CombineReality/Deck-X/Deck_X/STL_files/Display_Trays/with_inserts/dx_tray_50_r_0105.stl

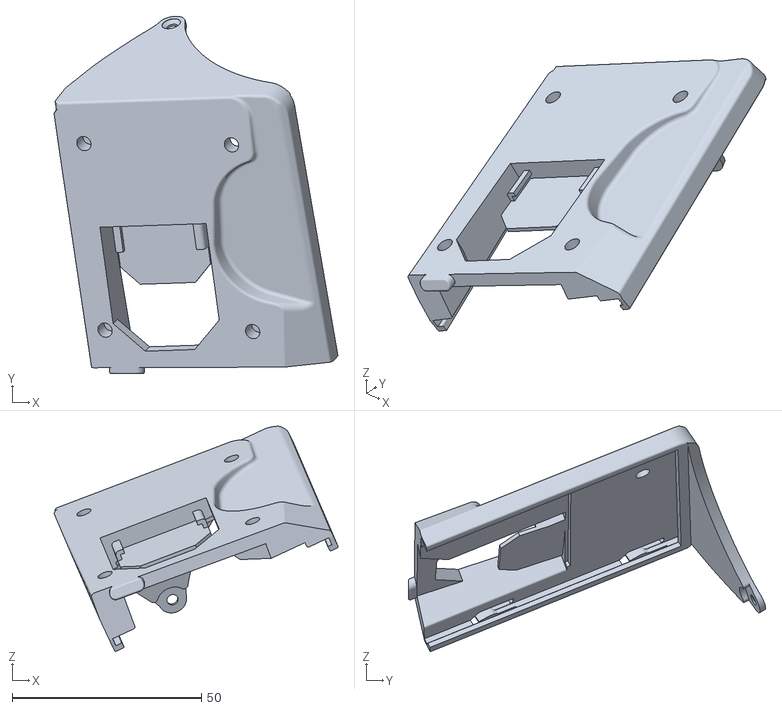
[picture p15: CAD file, 2021-03-06]
Deck_X/STL_files/Display_Trays/with_inserts/dx_tray_50_r_0105.stl
75.0 x 94.4 x 59.6
