CombineReality/Deck-X/Deck_X/STL_files/Headgear/dx_headgear_front_span.stl

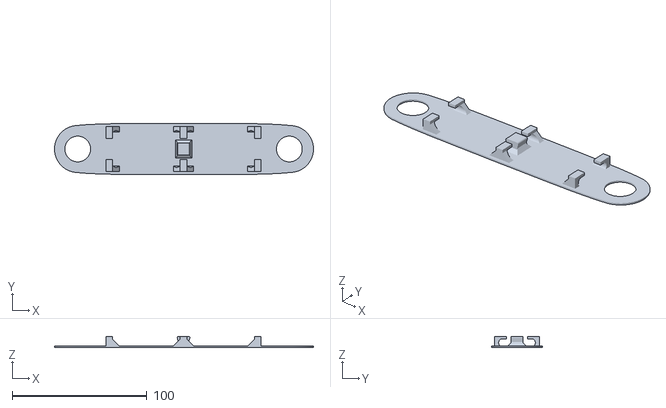
[picture p16: CAD file, 2021-03-06]
Deck_X/STL_files/Headgear/dx_headgear_front_span.stl
191.9 x 38.1 x 8.30
