CombineReality/Deck-X/Deck_X/STL_files/Headgear/Headgear_Pivots_(Print_2x)/dx_headgear_pivot_back_female.stl

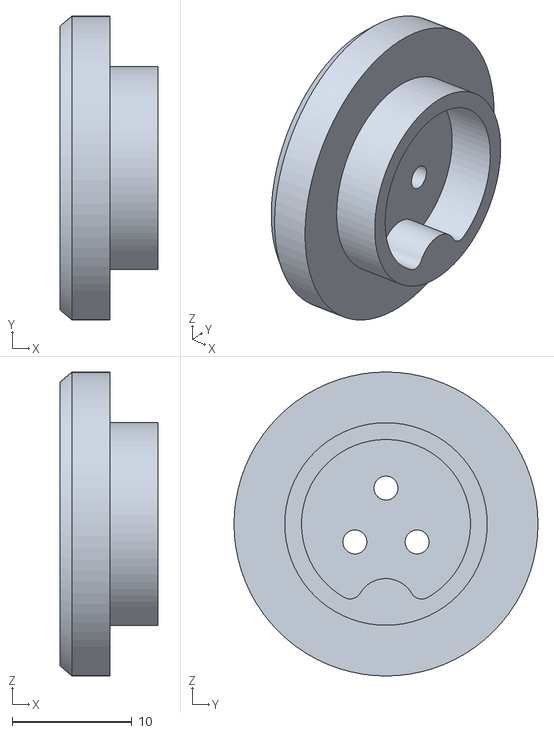
[picture p17: CAD file, 2021-03-06]
Deck_X/STL_files/Headgear/Headgear_Pivots_(Print_2x)/dx_headgear_pivot_back_female.stl
8.20 x 25.4 x 25.4
