CombineReality/Deck-X/Deck_X/STL_files/Lid_Assembly/dx_dpad_0105.stl

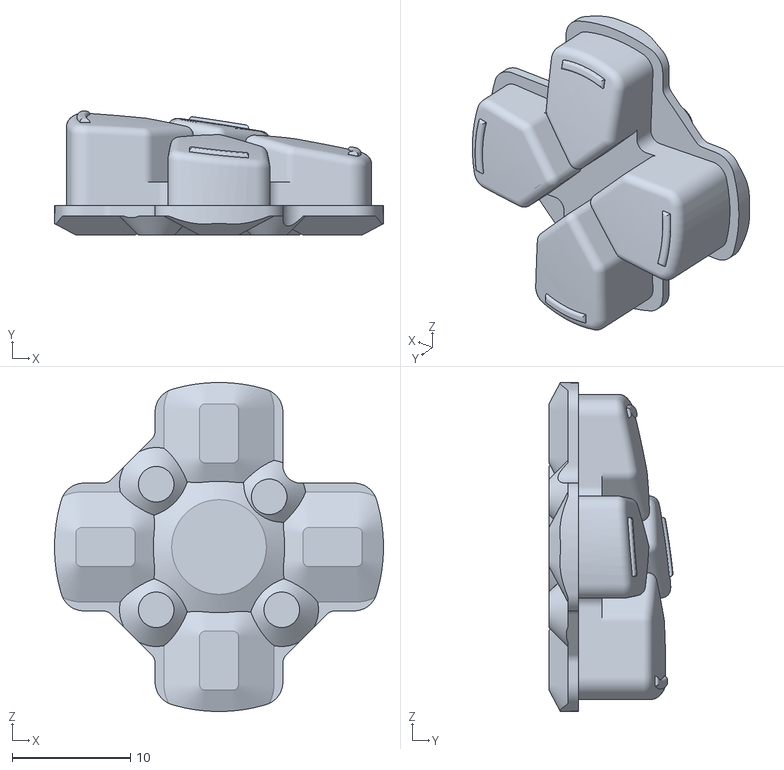
[picture p18: CAD file, 2021-03-06]
Deck_X/STL_files/Lid_Assembly/dx_dpad_0105.stl
27.8 x 10.5 x 27.8
