CombineReality/Deck-X/Calibration_Stand/#320-002 FDMI OPTIMIZED.stl

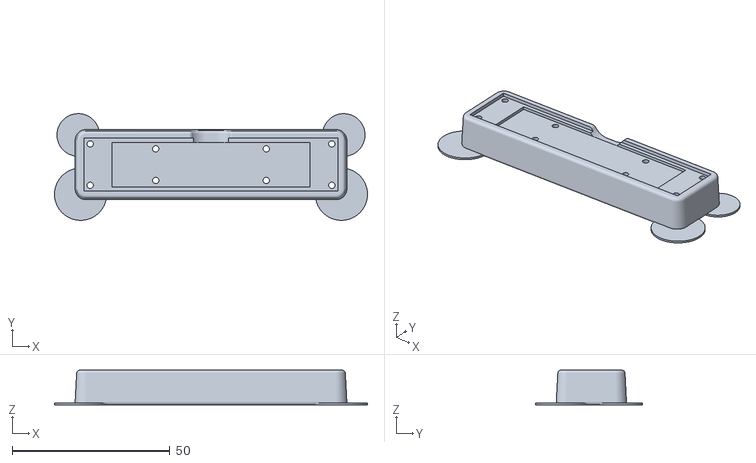
[picture p19: CAD file, 2020-12-14]
Calibration_Stand/#320-002 FDMI OPTIMIZED.stl
99.1 x 33.8 x 11.0
