CombineReality/Deck-X/Deck_X/STL_files/Headgear/dx_headgear_front.stl

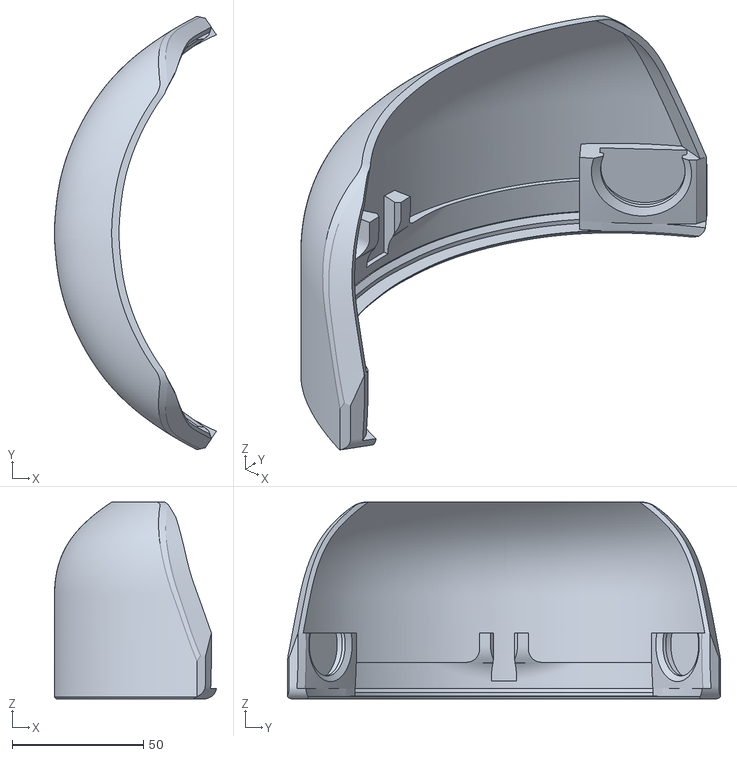
[picture p20: CAD file, 2021-03-06]
Deck_X/STL_files/Headgear/dx_headgear_front.stl
61.8 x 165.3 x 75.1
