CombineReality/Deck-X/Deck_X/STL_files/Headgear/Headgear_Pivots_(Print_2x)/dx_headgear_pivot_front_female.stl

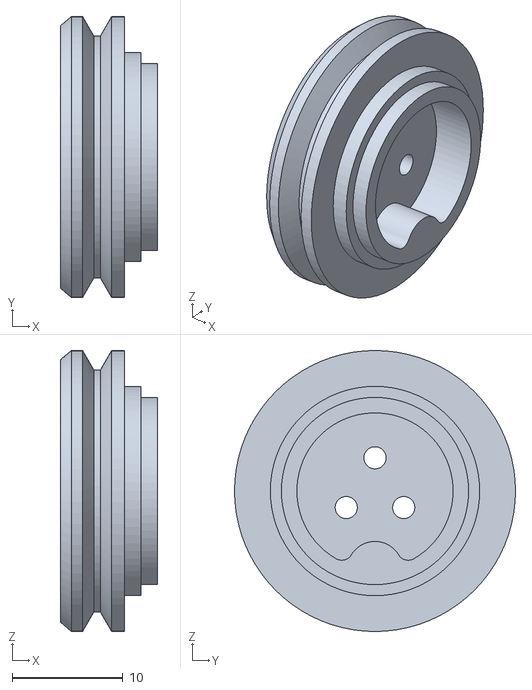
[picture p21: CAD file, 2021-03-06]
Deck_X/STL_files/Headgear/Headgear_Pivots_(Print_2x)/dx_headgear_pivot_front_female.stl
8.80 x 25.4 x 25.4
