CombineReality/Deck-X/Deck_X/STL_files/Optics_Bracket_Assembly/dx_forehead_pad_0105.stl

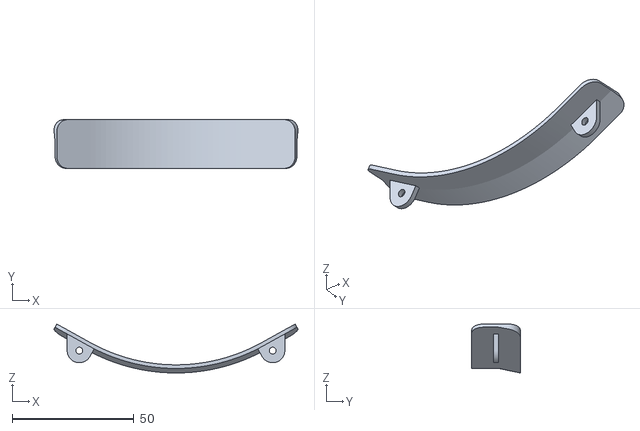
[picture p22: CAD file, 2021-03-06]
Deck_X/STL_files/Optics_Bracket_Assembly/dx_forehead_pad_0105.stl
100.3 x 20.0 x 20.1
