CombineReality/Deck-X/Calibration_Stand/#320-003 FDMI OPTIMIZED.stl

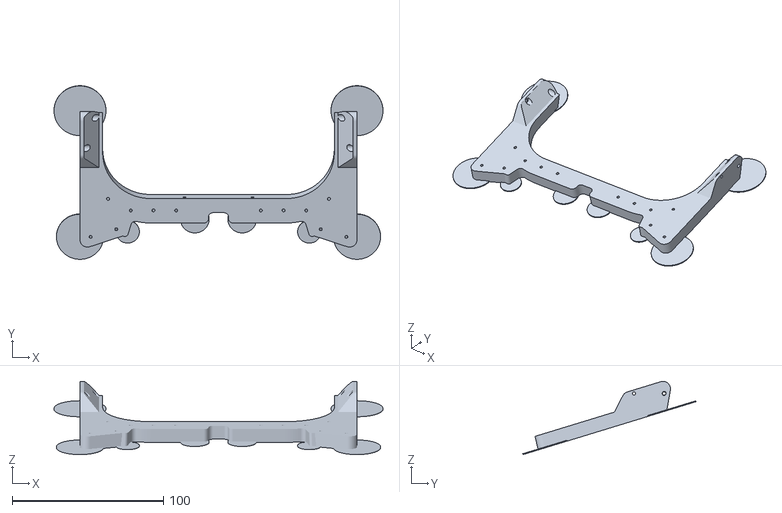
[picture p23: CAD file, 2020-12-14]
Calibration_Stand/#320-003 FDMI OPTIMIZED.stl
217.5 x 114.8 x 48.4
