CombineReality/Deck-X/Deck_X/STL_files/Headgear/dx_headgear_brake_cover_right.stl

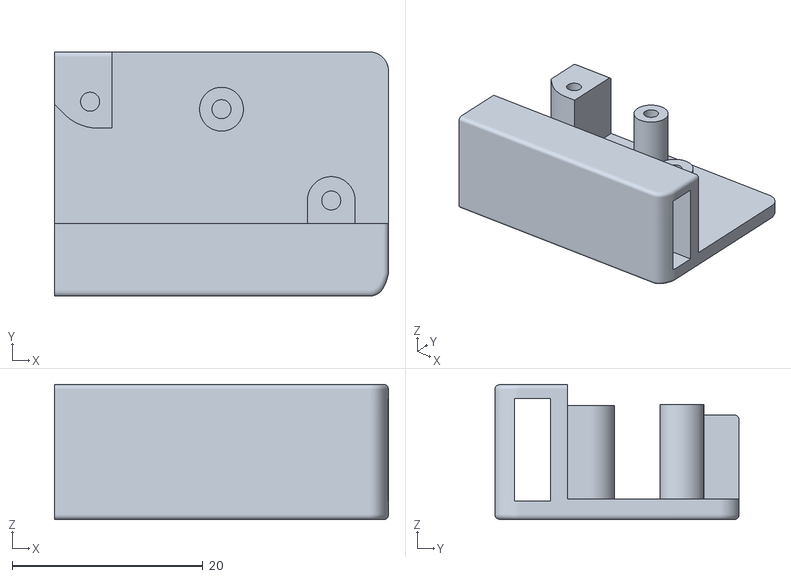
[picture p24: CAD file, 2021-03-06]
Deck_X/STL_files/Headgear/dx_headgear_brake_cover_right.stl
35.0 x 25.6 x 14.2
