CombineReality/Deck-X/Deck_X/STL_files/Optics_Bracket_Assembly/dx_leapmotion_spacer_0105.stl

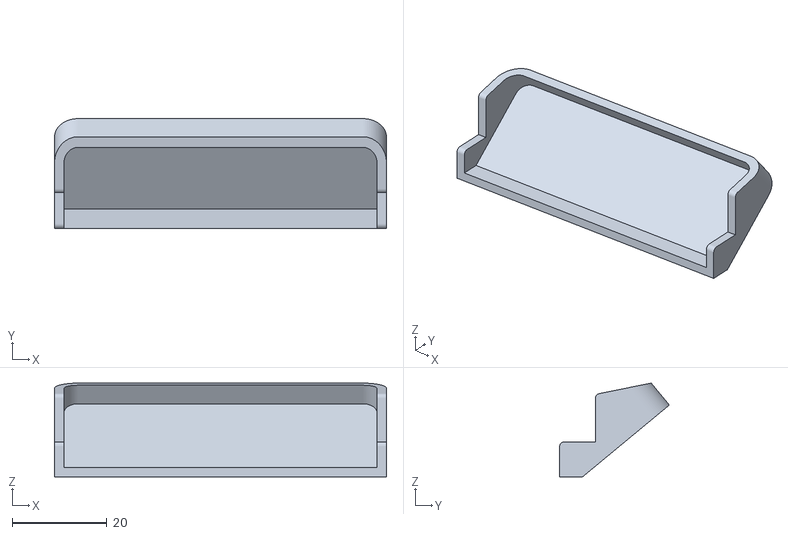
[picture p25: CAD file, 2021-03-06]
Deck_X/STL_files/Optics_Bracket_Assembly/dx_leapmotion_spacer_0105.stl
70.0 x 23.1 x 19.8
