CombineReality/Deck-X/Calibration_Stand/#310-001.stl

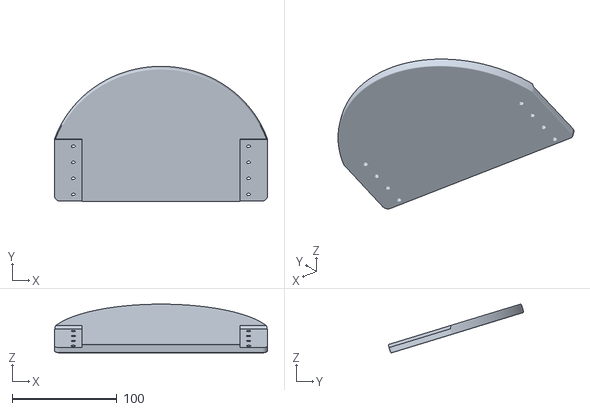
[picture p26: CAD file, 2020-12-14]
Calibration_Stand/#310-001.stl
203.1 x 129.0 x 46.5
