CombineReality/Deck-X/Deck_X/STL_files/Headgear/dx_headgear_hinge_l_0105.stl

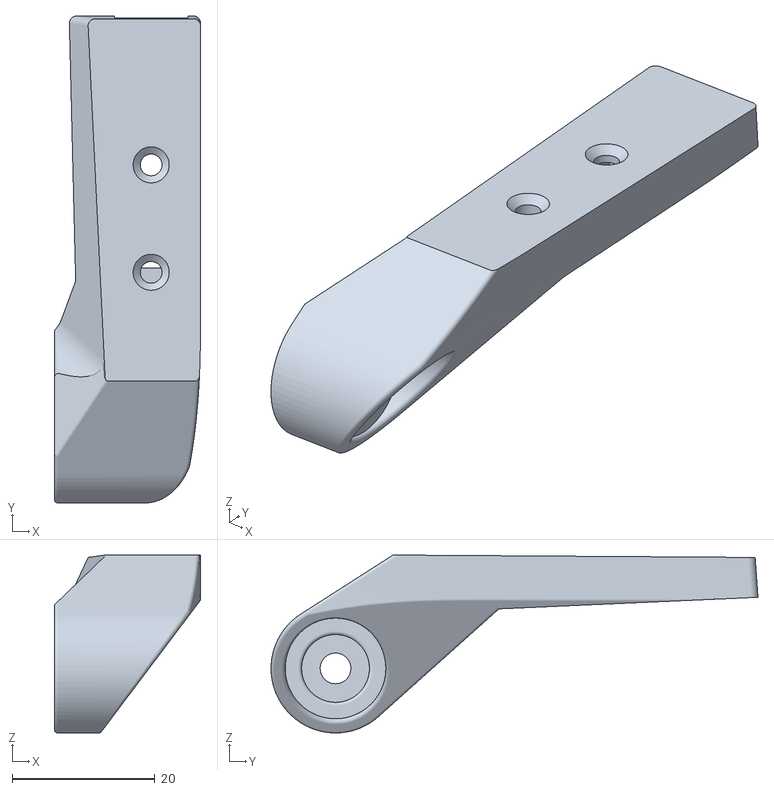
[picture p27: CAD file, 2021-03-06]
Deck_X/STL_files/Headgear/dx_headgear_hinge_l_0105.stl
20.5 x 68.3 x 24.9
