CombineReality/Deck-X/Calibration_Stand/#310-002 FDM OPTIMIZED.stl

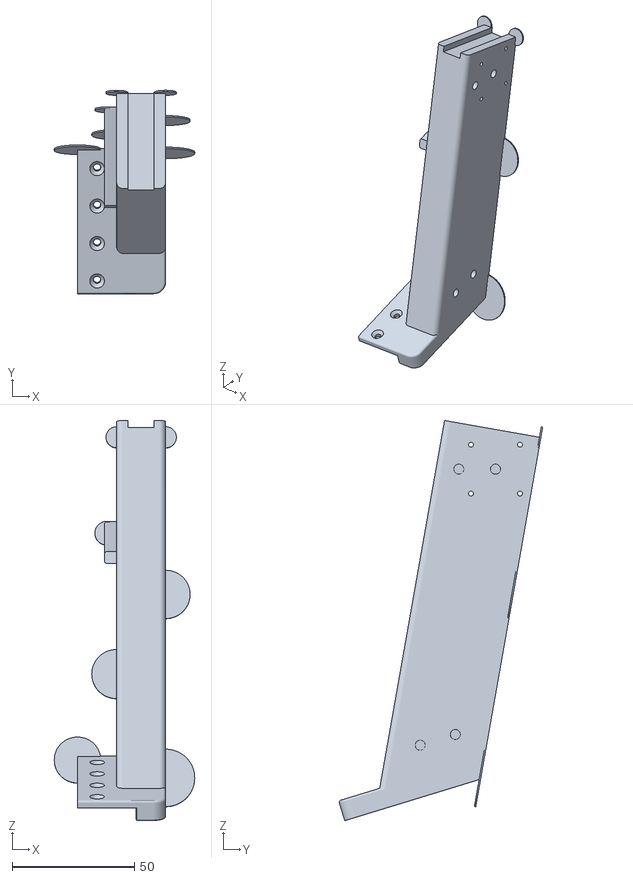
[picture p28: CAD file, 2020-12-14]
Calibration_Stand/#310-002 FDM OPTIMIZED.stl
57.4 x 83.2 x 163.5
