CombineReality/Deck-X/Calibration_Stand/#320-002.stl

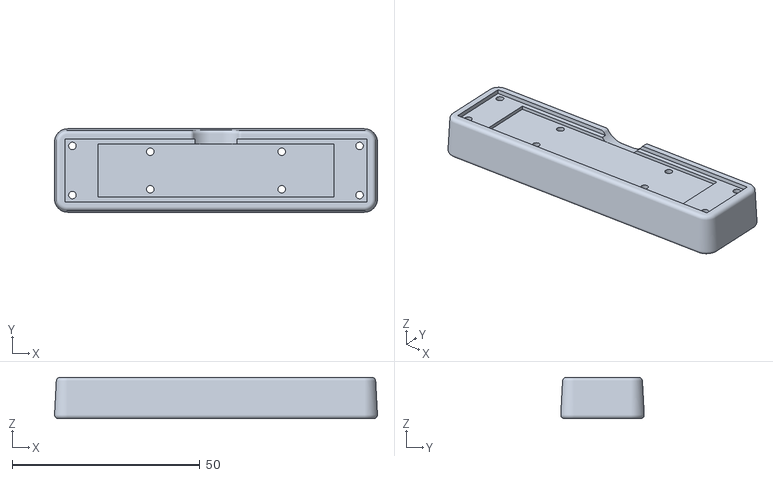
[picture p29: CAD file, 2020-12-14]
Calibration_Stand/#320-002.stl
86.0 x 22.2 x 11.0
