CombineReality/Deck-X/Calibration_Stand/#310-002.stl

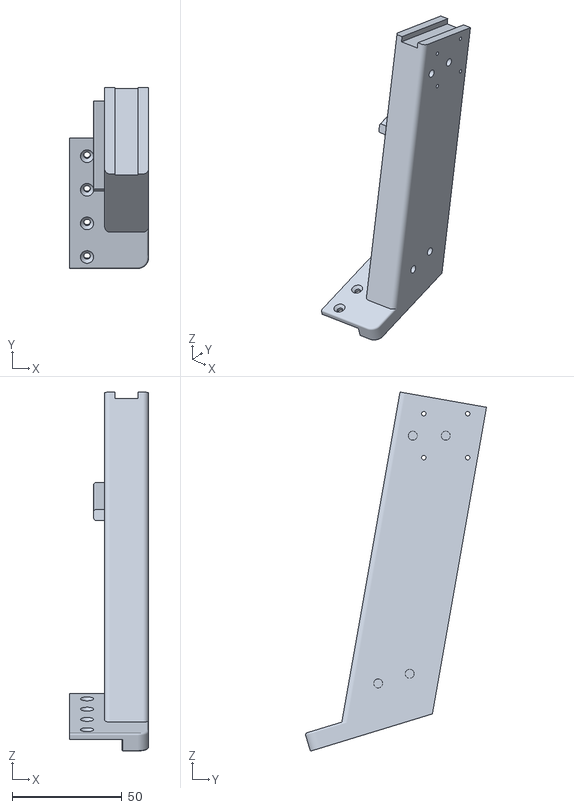
[picture p30: CAD file, 2020-12-14]
Calibration_Stand/#310-002.stl
36.0 x 82.4 x 163.5
