CombineReality/Deck-X/Deck_X/STL_files/Headgear/dx_headgear_brake_left.stl

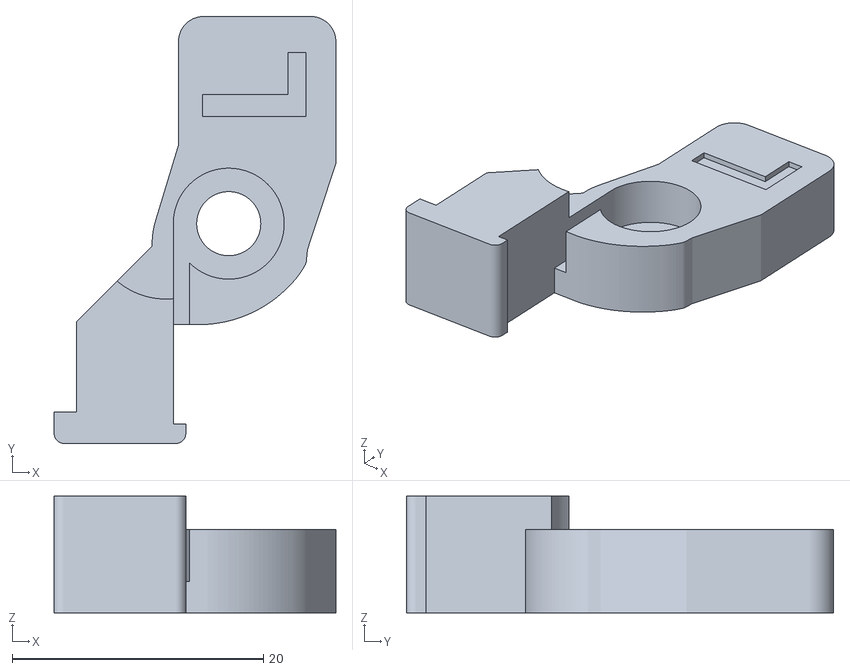
[picture p31: CAD file, 2021-03-06]
Deck_X/STL_files/Headgear/dx_headgear_brake_left.stl
22.4 x 34.0 x 9.30
